happychriss/GoodWatch_espif_ESP-NN/src/my_RTC_DS3231.cpp

#include <my_RTClib.h>
#include "support.h"

#define DS3231_ADDRESS 0x68   ///< I2C address for DS3231
#define DS3231_TIME 0x00      ///< Time register
#define DS3231_ALARM1 0x07    ///< Alarm 1 register
#define DS3231_ALARM2 0x0B    ///< Alarm 2 register
#define DS3231_CONTROL 0x0E   ///< Control register
#define DS3231_STATUSREG 0x0F ///< Status register
#define DS3231_TEMPERATUREREG                                                  \
  0x11 ///< Temperature register (high byte - low byte is at 0x12), 10-bit
///< temperature value

/**************************************************************************/
/*!
    @brief  Start I2C for the DS3231 and test succesful connection
    @param  wireInstance pointer to the I2C bus
    @return True if Wire can find DS3231 or false otherwise.
*/
/**************************************************************************/
boolean RTC_DS3231::begin(TwoWire *wireInstance) {
    if (i2c_dev)
        delete i2c_dev;
    i2c_dev = new Adafruit_I2CDevice(DS3231_ADDRESS, wireInstance);
    if (!i2c_dev->begin())
        return false;
    return true;
}

/**************************************************************************/
/*!
    @brief  Check the status register Oscillator Stop Flag to see if the DS3231
   stopped due to power loss
    @return True if the bit is set (oscillator stopped) or false if it is
   running
*/
/**************************************************************************/
bool RTC_DS3231::lostPower(void) {
    return read_register(DS3231_STATUSREG) >> 7;
}

/**************************************************************************/
/*!
    @brief  Set the date and flip the Oscillator Stop Flag
    @param dt DateTime object containing the date/time to set
*/
/**************************************************************************/
void RTC_DS3231::adjust(const DateTime &dt) {
    uint8_t buffer[8] = {DS3231_TIME,
                         bin2bcd(dt.second()),
                         bin2bcd(dt.minute()),
                         bin2bcd(dt.hour()),
                         bin2bcd(dowToDS3231(dt.dayOfTheWeek())),
                         bin2bcd(dt.day()),
                         bin2bcd(dt.month()),
                         bin2bcd(dt.year() - 2000U)};
    i2c_dev->write(buffer, 8);

    uint8_t statreg = read_register(DS3231_STATUSREG);
    statreg &= ~0x80; // flip OSF bit
    write_register(DS3231_STATUSREG, statreg);
}

/**************************************************************************/
/*!
    @brief  Get the current date/time
    @return DateTime object with the current date/time
*/
/**************************************************************************/
DateTime RTC_DS3231::now() {
    uint8_t buffer[7];
    buffer[0] = 0;
    i2c_dev->write_then_read(buffer, 1, buffer, 7);

    return DateTime(bcd2bin(buffer[6]) + 2000U, bcd2bin(buffer[5] & 0x7F),
                    bcd2bin(buffer[4]), bcd2bin(buffer[2]), bcd2bin(buffer[1]),
                    bcd2bin(buffer[0] & 0x7F));
}

/**************************************************************************/
/*!
    @brief  Read the SQW pin mode
    @return Pin mode, see Ds3231SqwPinMode enum
*/
/**************************************************************************/
Ds3231SqwPinMode RTC_DS3231::readSqwPinMode() {
    int mode;
    mode = read_register(DS3231_CONTROL) & 0x1C;
    if (mode & 0x04)
        mode = DS3231_OFF;
    return static_cast<Ds3231SqwPinMode>(mode);
}

/**************************************************************************/
/*!
    @brief  Set the SQW pin mode
    @param mode Desired mode, see Ds3231SqwPinMode enum
*/
/**************************************************************************/
void RTC_DS3231::writeSqwPinMode(Ds3231SqwPinMode mode) {
    uint8_t ctrl = read_register(DS3231_CONTROL);

    ctrl &= ~0x04; // turn off INTCON
    ctrl &= ~0x18; // set freq bits to 0

    write_register(DS3231_CONTROL, ctrl | mode);
}

/**************************************************************************/
/*!
    @brief  Get the current temperature from the DS3231's temperature sensor
    @return Current temperature (float)
*/
/**************************************************************************/
float RTC_DS3231::getTemperature() {
    uint8_t buffer[2] = {DS3231_TEMPERATUREREG, 0};
    i2c_dev->write_then_read(buffer, 1, buffer, 2);
    return (float) buffer[0] + (buffer[1] >> 6) * 0.25f;
}

/**************************************************************************/
/*!
    @brief  Set alarm 1 for DS3231
        @param 	dt DateTime object
        @param 	alarm_mode Desired mode, see Ds3231Alarm1Mode enum
    @return False if control register is not set, otherwise true
*/
/**************************************************************************/
bool RTC_DS3231::setAlarm1(const DateTime &dt, Ds3231Alarm1Mode alarm_mode) {
    uint8_t ctrl = read_register(DS3231_CONTROL);
    if (!(ctrl & 0x04)) {
        return false;
    }

    uint8_t A1M1 = (alarm_mode & 0x01) << 7; // Seconds bit 7.
    uint8_t A1M2 = (alarm_mode & 0x02) << 6; // Minutes bit 7.
    uint8_t A1M3 = (alarm_mode & 0x04) << 5; // Hour bit 7.
    uint8_t A1M4 = (alarm_mode & 0x08) << 4; // Day/Date bit 7.
    uint8_t DY_DT = (alarm_mode & 0x10)
            << 2; // Day/Date bit 6. Date when 0, day of week when 1.
    uint8_t day = (DY_DT) ? dowToDS3231(dt.dayOfTheWeek()) : dt.day();

    uint8_t buffer[5] = {DS3231_ALARM1, uint8_t(bin2bcd(dt.second()) | A1M1),
                         uint8_t(bin2bcd(dt.minute()) | A1M2),
                         uint8_t(bin2bcd(dt.hour()) | A1M3),
                         uint8_t(bin2bcd(day) | A1M4 | DY_DT)};
    i2c_dev->write(buffer, 5);

    write_register(DS3231_CONTROL, ctrl | 0x01); // AI1E

    return true;
}

/**************************************************************************/
/*!
    @brief  Set alarm 2 for DS3231
        @param 	dt DateTime object
        @param 	alarm_mode Desired mode, see Ds3231Alarm2Mode enum
    @return False if control register is not set, otherwise true
*/
/**************************************************************************/
bool RTC_DS3231::setAlarm2(const DateTime &dt, Ds3231Alarm2Mode alarm_mode) {
    uint8_t ctrl = read_register(DS3231_CONTROL);
    if (!(ctrl & 0x04)) {
        DPL("ERROR: I2C Read Control Register");
        return false;
    }

    uint8_t A2M2 = (alarm_mode & 0x01) << 7; // Minutes bit 7.
    uint8_t A2M3 = (alarm_mode & 0x02) << 6; // Hour bit 7.
    uint8_t A2M4 = (alarm_mode & 0x04) << 5; // Day/Date bit 7.
    uint8_t DY_DT = (alarm_mode & 0x08)
            << 3; // Day/Date bit 6. Date when 0, day of week when 1.
    uint8_t day = (DY_DT) ? dowToDS3231(dt.dayOfTheWeek()) : dt.day();

    uint8_t buffer[4] = {DS3231_ALARM2, uint8_t(bin2bcd(dt.minute()) | A2M2),
                         uint8_t(bin2bcd(dt.hour()) | A2M3),
                         uint8_t(bin2bcd(day) | A2M4 | DY_DT)};

    if (!(i2c_dev->write(buffer, 4))) {
        DPL("ERROR: I2C Write Buffer");
        return false;
    };

    write_register(DS3231_CONTROL, ctrl | 0x02); // AI2E

    return true;
}

/**************************************************************************/
/*!
    @brief  Disable alarm
        @param 	alarm_num Alarm number to disable
*/
/**************************************************************************/
void RTC_DS3231::disableAlarm(uint8_t alarm_num) {
    uint8_t ctrl = read_register(DS3231_CONTROL);
    ctrl &= ~(1 << (alarm_num - 1));
    write_register(DS3231_CONTROL, ctrl);
}

/**************************************************************************/
/*!
    @brief  Clear status of alarm
        @param 	alarm_num Alarm number to clear
*/
/**************************************************************************/
void RTC_DS3231::clearAlarm(uint8_t alarm_num) {
    uint8_t status = read_register(DS3231_STATUSREG);
    status &= ~(0x1 << (alarm_num - 1));
    write_register(DS3231_STATUSREG, status);
}

/**************************************************************************/
/*!
    @brief  Get status of alarm
        @param 	alarm_num Alarm number to check status of
        @return True if alarm has been fired otherwise false
*/
/**************************************************************************/
bool RTC_DS3231::alarmFired(uint8_t alarm_num) {
    return (read_register(DS3231_STATUSREG) >> (alarm_num - 1)) & 0x1;
}

/**************************************************************************/
/*!
    @brief  Enable 32KHz Output
    @details The 32kHz output is enabled by default. It requires an external
    pull-up resistor to function correctly
*/
/**************************************************************************/
void RTC_DS3231::enable32K(void) {
    uint8_t status = read_register(DS3231_STATUSREG);
    status |= (0x1 << 0x03);
    write_register(DS3231_STATUSREG, status);
}

/**************************************************************************/
/*!
    @brief  Disable 32KHz Output
*/
/**************************************************************************/
void RTC_DS3231::disable32K(void) {
    uint8_t status = read_register(DS3231_STATUSREG);
    status &= ~(0x1 << 0x03);
    write_register(DS3231_STATUSREG, status);
}

/**************************************************************************/
/*!
    @brief  Get status of 32KHz Output
    @return True if enabled otherwise false
*/
/**************************************************************************/
bool RTC_DS3231::isEnabled32K(void) {
    return (read_register(DS3231_STATUSREG) >> 0x03) & 0x01;
}


bool RTC_DS3231::getAlarm2(DateTime *alarm, DateTime current_time) {

    DPL("Check Alarm2");
#define BM_ALARM_2_ENABLED  0b00000010
    uint8_t c = read_register(DS3231_CONTROL);
    boolean cc = (c & BM_ALARM_2_ENABLED) >> 1;

    if (cc) {
        DPL("Alarm2 is enabled!");
    } else {
        DPL("Alarm2 is disabled!");
    }

    uint8_t buffer[3] = {DS3231_ALARM2, 121, 122};
    if(!(i2c_dev->write_then_read(buffer, 1, buffer, 3,false))) {
        DPL("ERROR WRITE");
    }

    uint8_t m = buffer[0];
    uint8_t h = buffer[1];
    uint8_t d = buffer[2];

#define  BM_01_MIN 0b00001111
#define  BM_10_MIN 0b01110000
    uint8_t mm = (m & BM_01_MIN) + 10 * ((m & BM_10_MIN) >> 4);

#define BM_01_HH 0b00001111
#define BM_10_HH 0b00010000
#define BM_20_HH 0b00100000
    uint8_t hh = (h & BM_01_HH) + 10 * ((h & BM_10_HH) >> 4) + 20 * ((h & BM_20_HH) >> 5);

    // !!! Assuming date alarm is active
#define BM_01_DATE 0b00001111
#define BM_10_DATE 0b00110000
    uint8_t dd = (d & BM_01_DATE) + 10 * ((d & BM_10_DATE) >> 4);

    uint16_t yy = current_time.year();
    uint8_t mo = current_time.month();

    // Alarm clock does not know month, we can take current month/year - if alarm is on next month/month end, we need to jump to next month
    if (current_time.day() > dd) {
        mo++;
        if (mo > 12) {
            mo = 1;
            yy++;
        }
    }
    *alarm = DateTime(yy, mo, dd, hh, mm, 0);

    DPL("***********************");
    DPF("M:%i H:%i D:%i\n", m, h, d);
    DPF("%i:%i  - DD:%i MM:%i YY:%i \n", hh, mm, dd, mm, yy);
    DPL("***********************");

    return cc;

}


bool RTC_DS3231::getAlarm1(DateTime *alarm, DateTime current_time) {
    DPL("Check Alarm1");
#define BM_ALARM_2_ENABLED  0b00000010
#define BM_ALARM_1_ENABLED  0b00000001
    uint8_t c = read_register(DS3231_CONTROL);
    boolean cc = (c & BM_ALARM_1_ENABLED) ;

    if (cc) {
        DPL("Alarm1 is enabled!");
    } else {
        DPL("Alarm1 is disabled!");
    }


    uint8_t buffer[5] = {DS3231_ALARM1, 0, 0, 0,0};
    i2c_dev->write_then_read(buffer, 1, buffer, 3);

    uint8_t s = buffer[1];
    uint8_t m = buffer[2];
    uint8_t h = buffer[3];
    uint8_t d = buffer[4];

    DPF("Alarm1 s:%i,m:%i h:%i d:%i\n", s, m, h, d);

#define  BM_01_MIN 0b00001111
#define  BM_10_MIN 0b01110000
    uint8_t ss = (s & BM_01_MIN) + 10 * ((s & BM_10_MIN) >> 4);

#define  BM_01_MIN 0b00001111
#define  BM_10_MIN 0b01110000
    uint8_t mm = (m & BM_01_MIN) + 10 * ((m & BM_10_MIN) >> 4);

#define BM_01_HH 0b00001111
#define BM_10_HH 0b00010000
#define BM_20_HH 0b00100000
    uint8_t hh = (h & BM_01_HH) + 10 * ((h & BM_10_HH) >> 4) + 20 * ((h & BM_20_HH) >> 5);

    // !!! Assuming date alarm is active
#define BM_01_DATE 0b00001111
#define BM_10_DATE 0b00110000
    uint8_t dd = (d & BM_01_DATE) + 10 * ((d & BM_10_DATE) >> 4);

    uint16_t yy = current_time.year();
    uint8_t mo = current_time.month();

    // Alarm clock does not know month, we can take current month/year - if alarm is on next month/month end, we need to jump to next month
    if (current_time.day() > dd) {
        mo++;
        if (mo > 12) {
            mo = 1;
            yy++;
        }
    }
    *alarm = DateTime(yy, mo, dd, hh, mm, ss);

//        DPL("***********************");
    Serial.printf("S:%i M:%i H:%i D:%i\n", s,m, h, d);
    Serial.printf("%i:%i:%i  - DD:%i MO:%i YY:%i \n", hh, mm,ss, dd, mo, yy);
    DPL("***********************");

    return cc;

}
