happychriss/GoodWatch_espif_ESP-NN/include/GxEPD2_display_selection_new_style.h

// Display Library example for SPI e-paper panels from Dalian Good Display and boards from Waveshare.
// Requires HW SPI and Adafruit_GFX. Caution: the e-paper panels require 3.3V supply AND data lines!
//
// Display Library based on Demo Example from Good Display: http://www.e-paper-display.com/download_list/downloadcategoryid=34&isMode=false.html
//
// Author: Jean-Marc Zingg
//
// Version: see library.properties
//
// Library: https://github.com/ZinggJM/GxEPD2

// Supporting Arduino Forum Topics:
// Waveshare e-paper displays with SPI: http://forum.arduino.cc/index.php?topic=487007.0
// Good Display ePaper for Arduino: https://forum.arduino.cc/index.php?topic=436411.0

// select the display class (only one), matching the kind of display panel

//#undef DISABLE_DIAGNOSTIC_OUTPUT

#define GxEPD2_DISPLAY_CLASS GxEPD2_BW
//#define GxEPD2_DISPLAY_CLASS GxEPD2_3C
//#define GxEPD2_DISPLAY_CLASS GxEPD2_7C

// select the display driver class (only one) for your  panel
//#define GxEPD2_DRIVER_CLASS GxEPD2_154     // GDEP015OC1  200x200, no longer available
//#define GxEPD2_DRIVER_CLASS GxEPD2_154_D67 // GDEH0154D67 200x200
//#define GxEPD2_DRIVER_CLASS GxEPD2_154_T8  // GDEW0154T8  152x152
//#define GxEPD2_DRIVER_CLASS GxEPD2_154_M09 // GDEW0154M09 200x200
//#define GxEPD2_DRIVER_CLASS GxEPD2_154_M10 // GDEW0154M10 152x152
//#define GxEPD2_DRIVER_CLASS GxEPD2_213     // GDE0213B1   128x250, phased out
//#define GxEPD2_DRIVER_CLASS GxEPD2_213_B72 // GDEH0213B72 128x250
//#define GxEPD2_DRIVER_CLASS GxEPD2_213_B73 // GDEH0213B73 128x250
//#define GxEPD2_DRIVER_CLASS GxEPD2_213_flex // GDEW0213I5F 104x212
//#define GxEPD2_DRIVER_CLASS GxEPD2_213_M21 // GDEW0213M21 104x212
//#define GxEPD2_DRIVER_CLASS GxEPD2_213_T5D // GDEW0213T5D 104x212
//#define GxEPD2_DRIVER_CLASS GxEPD2_290     // GDEH029A1   128x296
//#define GxEPD2_DRIVER_CLASS GxEPD2_290_T5  // GDEW029T5   128x296
//#define GxEPD2_DRIVER_CLASS GxEPD2_290_T5D // GDEW029T5D  128x296
//#define GxEPD2_DRIVER_CLASS GxEPD2_290_T94 // GDEM029T94  128x296
//#define GxEPD2_DRIVER_CLASS GxEPD2_290_M06 // GDEW029M06  128x296
//#define GxEPD2_DRIVER_CLASS GxEPD2_260     // GDEW026T0   152x296
//#define GxEPD2_DRIVER_CLASS GxEPD2_260_M01 // GDEW026M01  152x296
//#define GxEPD2_DRIVER_CLASS GxEPD2_270     // GDEW027W3   176x264
//#define GxEPD2_DRIVER_CLASS GxEPD2_371     // GDEW0371W7  240x416
#define GxEPD2_DRIVER_CLASS GxEPD2_420     // GDEW042T2   400x300
//#define GxEPD2_DRIVER_CLASS GxEPD2_420_M01 // GDEW042M01  400x300
//#define GxEPD2_DRIVER_CLASS GxEPD2_583     // GDEW0583T7  600x448
//#define GxEPD2_DRIVER_CLASS GxEPD2_583_T8  // GDEW0583T8  648x480
//#define GxEPD2_DRIVER_CLASS GxEPD2_750     // GDEW075T8   640x384
//#define GxEPD2_DRIVER_CLASS GxEPD2_750_T7  // GDEW075T7   800x480
// 3-color e-papers
//#define GxEPD2_DRIVER_CLASS GxEPD2_154c     // GDEW0154Z04 200x200, no longer available
//#define GxEPD2_DRIVER_CLASS GxEPD2_154_Z90c // GDEH0154Z90 200x200
//#define GxEPD2_DRIVER_CLASS GxEPD2_213c     // GDEW0213Z16 104x212
//#define GxEPD2_DRIVER_CLASS GxEPD2_213_Z19c // GDEW0213Z19 104x212
//#define GxEPD2_DRIVER_CLASS GxEPD2_290c     // GDEW029Z10  128x296
//#define GxEPD2_DRIVER_CLASS GxEPD2_290_Z13c // GDEH029Z13  128x296
//#define GxEPD2_DRIVER_CLASS GxEPD2_290_C90c // GDEM029C90  128x296
//#define GxEPD2_DRIVER_CLASS GxEPD2_270c     // GDEW027C44  176x264
//#define GxEPD2_DRIVER_CLASS GxEPD2_420c     // GDEW042Z15  400x300
//#define GxEPD2_DRIVER_CLASS GxEPD2_583c     // GDEW0583Z21 600x448
//#define GxEPD2_DRIVER_CLASS GxEPD2_750c     // GDEW075Z09  640x384
//#define GxEPD2_DRIVER_CLASS GxEPD2_750c_Z08 // GDEW075Z08  800x480
//#define GxEPD2_DRIVER_CLASS GxEPD2_750c_Z90 // GDEH075Z90  880x528
//#define GxEPD2_DRIVER_CLASS GxEPD2_1248     // GDEW1248T3  1303x984
// 7-color e-paper
//#define GxEPD2_DRIVER_CLASS GxEPD2_565c // Waveshare 5.65" 7-color (3C graphics)
// grey levels parallel IF e-papers on Waveshare e-Paper IT8951 Driver HAT
//#define GxEPD2_DRIVER_CLASS GxEPD2_it60           // ED060SCT 800x600
//#define GxEPD2_DRIVER_CLASS GxEPD2_it60_1448x1072 // ED060KC1 1448x1072

// SS is usually used for CS. define here for easy change
#include <global_hardware.h>


#ifndef EPD_CS
#define EPD_CS SS
#endif

#if defined(GxEPD2_DISPLAY_CLASS) && defined(GxEPD2_DRIVER_CLASS)

// somehow there should be an easier way to do this
#define GxEPD2_BW_IS_GxEPD2_BW true
#define GxEPD2_3C_IS_GxEPD2_3C true
#define GxEPD2_7C_IS_GxEPD2_7C true
#define GxEPD2_1248_IS_GxEPD2_1248 true
#define IS_GxEPD(c, x) (c##x)
#define IS_GxEPD2_BW(x) IS_GxEPD(GxEPD2_BW_IS_, x)
#define IS_GxEPD2_3C(x) IS_GxEPD(GxEPD2_3C_IS_, x)
#define IS_GxEPD2_7C(x) IS_GxEPD(GxEPD2_7C_IS_, x)
#define IS_GxEPD2_1248(x) IS_GxEPD(GxEPD2_1248_IS_, x)

#include "GxEPD2_selection_check.h"

#if defined (ESP8266)
#define MAX_DISPLAY_BUFFER_SIZE (81920ul-34000ul-5000ul) // ~34000 base use, change 5000 to your application use
#if IS_GxEPD2_BW(GxEPD2_DISPLAY_CLASS)
#define MAX_HEIGHT(EPD) (EPD::HEIGHT <= MAX_DISPLAY_BUFFER_SIZE / (EPD::WIDTH / 8) ? EPD::HEIGHT : MAX_DISPLAY_BUFFER_SIZE / (EPD::WIDTH / 8))
#elif IS_GxEPD2_3C(GxEPD2_DISPLAY_CLASS)
#define MAX_HEIGHT(EPD) (EPD::HEIGHT <= (MAX_DISPLAY_BUFFER_SIZE / 2) / (EPD::WIDTH / 8) ? EPD::HEIGHT : (MAX_DISPLAY_BUFFER_SIZE / 2) / (EPD::WIDTH / 8))
#elif IS_GxEPD2_7C(GxEPD2_DISPLAY_CLASS)
#define MAX_HEIGHT(EPD) (EPD::HEIGHT <= (MAX_DISPLAY_BUFFER_SIZE) / (EPD::WIDTH / 2) ? EPD::HEIGHT : (MAX_DISPLAY_BUFFER_SIZE) / (EPD::WIDTH / 2))
#endif
// adapt the constructor parameters to your wiring
GxEPD2_DISPLAY_CLASS<GxEPD2_DRIVER_CLASS, MAX_HEIGHT(GxEPD2_DRIVER_CLASS)> display(GxEPD2_DRIVER_CLASS(/*CS=D8*/ EPD_CS, /*DC=D3*/ 0, /*RST=D4*/ 2, /*BUSY=D2*/ 4));
// mapping of Waveshare e-Paper ESP8266 Driver Board, new version
//GxEPD2_DISPLAY_CLASS<GxEPD2_DRIVER_CLASS, MAX_HEIGHT(GxEPD2_DRIVER_CLASS)> display(GxEPD2_DRIVER_CLASS(/*CS=15*/ EPD_CS, /*DC=4*/ 4, /*RST=2*/ 2, /*BUSY=5*/ 5));
// mapping of Waveshare e-Paper ESP8266 Driver Board, old version
//GxEPD2_DISPLAY_CLASS<GxEPD2_DRIVER_CLASS, MAX_HEIGHT(GxEPD2_DRIVER_CLASS)> display(GxEPD2_DRIVER_CLASS(/*CS=15*/ EPD_CS, /*DC=4*/ 4, /*RST=5*/ 5, /*BUSY=16*/ 16));
#endif

#if defined(ESP32)
#define MAX_DISPLAY_BUFFER_SIZE 65536ul // e.g.
#if IS_GxEPD2_BW(GxEPD2_DISPLAY_CLASS)
#define MAX_HEIGHT(EPD) (EPD::HEIGHT <= MAX_DISPLAY_BUFFER_SIZE / (EPD::WIDTH / 8) ? EPD::HEIGHT : MAX_DISPLAY_BUFFER_SIZE / (EPD::WIDTH / 8))
#elif IS_GxEPD2_3C(GxEPD2_DISPLAY_CLASS)
#define MAX_HEIGHT(EPD) (EPD::HEIGHT <= (MAX_DISPLAY_BUFFER_SIZE / 2) / (EPD::WIDTH / 8) ? EPD::HEIGHT : (MAX_DISPLAY_BUFFER_SIZE / 2) / (EPD::WIDTH / 8))
#elif IS_GxEPD2_7C(GxEPD2_DISPLAY_CLASS)
#define MAX_HEIGHT(EPD) (EPD::HEIGHT <= (MAX_DISPLAY_BUFFER_SIZE) / (EPD::WIDTH / 2) ? EPD::HEIGHT : (MAX_DISPLAY_BUFFER_SIZE) / (EPD::WIDTH / 2))
#endif
// adapt the constructor parameters to your wiring
#if !IS_GxEPD2_1248(GxEPD2_DRIVER_CLASS)
#if defined(ARDUINO_LOLIN_D32_PRO)
GxEPD2_DISPLAY_CLASS<GxEPD2_DRIVER_CLASS, MAX_HEIGHT(GxEPD2_DRIVER_CLASS)> display(GxEPD2_DRIVER_CLASS(/*CS=5*/ EPD_CS, /*DC=*/ EPD_DC, /*RST=*/ EPD_RST, /*BUSY=*/ EPD_BUSY));
#elif defined(ARDUINO_ESP32_DEV) // e.g. TTGO T8 ESP32-WROVER
GxEPD2_DISPLAY_CLASS<GxEPD2_DRIVER_CLASS, MAX_HEIGHT(GxEPD2_DRIVER_CLASS)> display(GxEPD2_DRIVER_CLASS(/*CS=5*/ EPD_CS, /*DC=*/ 2, /*RST=*/ 0, /*BUSY=*/ 4));
#else
GxEPD2_DISPLAY_CLASS<GxEPD2_DRIVER_CLASS, MAX_HEIGHT(GxEPD2_DRIVER_CLASS)> display(GxEPD2_DRIVER_CLASS(/*CS=5*/ EPD_CS, /*DC=*/ 17, /*RST=*/ 16, /*BUSY=*/ 4));
#endif
#else // GxEPD2_1248
// Waveshare 12.48 b/w SPI display board and frame or Good Display 12.48 b/w panel GDEW1248T3
// general constructor for use with all parameters, e.g. for Waveshare ESP32 driver board mounted on connection board
GxEPD2_BW < GxEPD2_1248, GxEPD2_1248::HEIGHT / 4 > display(GxEPD2_1248(/*sck=*/ 13, /*miso=*/ 12, /*mosi=*/ 14,
    /*cs_m1=*/ 23, /*cs_s1=*/ 22, /*cs_m2=*/ 16, /*cs_s2=*/ 19,
    /*dc1=*/ 25, /*dc2=*/ 17, /*rst1=*/ 33, /*rst2=*/ 5,
    /*busy_m1=*/ 32, /*busy_s1=*/ 26, /*busy_m2=*/ 18, /*busy_s2=*/ 4));
#endif
#endif

// can't use package "STMF1 Boards (STM32Duino.com)" (Roger Clark) anymore with Adafruit_GFX, use "STM32 Boards (selected from submenu)" (STMicroelectronics)
#if defined(ARDUINO_ARCH_STM32)
#define MAX_DISPLAY_BUFFER_SIZE 15000ul // ~15k is a good compromise
#if IS_GxEPD2_BW(GxEPD2_DISPLAY_CLASS)
#define MAX_HEIGHT(EPD) (EPD::HEIGHT <= MAX_DISPLAY_BUFFER_SIZE / (EPD::WIDTH / 8) ? EPD::HEIGHT : MAX_DISPLAY_BUFFER_SIZE / (EPD::WIDTH / 8))
#elif IS_GxEPD2_3C(GxEPD2_DISPLAY_CLASS)
#define MAX_HEIGHT(EPD) (EPD::HEIGHT <= (MAX_DISPLAY_BUFFER_SIZE / 2) / (EPD::WIDTH / 8) ? EPD::HEIGHT : (MAX_DISPLAY_BUFFER_SIZE / 2) / (EPD::WIDTH / 8))
#elif IS_GxEPD2_7C(GxEPD2_DISPLAY_CLASS)
#define MAX_HEIGHT(EPD) (EPD::HEIGHT <= (MAX_DISPLAY_BUFFER_SIZE) / (EPD::WIDTH / 2) ? EPD::HEIGHT : (MAX_DISPLAY_BUFFER_SIZE) / (EPD::WIDTH / 2))
#endif
// adapt the constructor parameters to your wiring
GxEPD2_DISPLAY_CLASS<GxEPD2_DRIVER_CLASS, MAX_HEIGHT(GxEPD2_DRIVER_CLASS)> display(GxEPD2_DRIVER_CLASS(/*CS=4*/ EPD_CS, /*DC=*/ 3, /*RST=*/ 2, /*BUSY=*/ 1));
#endif

#if defined(__AVR)
#if defined (ARDUINO_AVR_MEGA2560) // Note: SS is on 53 on MEGA
#define MAX_DISPLAY_BUFFER_SIZE 5000 // e.g. full height for 200x200
#else // Note: SS is on 10 on UNO, NANO
#define MAX_DISPLAY_BUFFER_SIZE 800 // 
#endif
#if IS_GxEPD2_BW(GxEPD2_DISPLAY_CLASS)
#define MAX_HEIGHT(EPD) (EPD::HEIGHT <= MAX_DISPLAY_BUFFER_SIZE / (EPD::WIDTH / 8) ? EPD::HEIGHT : MAX_DISPLAY_BUFFER_SIZE / (EPD::WIDTH / 8))
#elif IS_GxEPD2_3C(GxEPD2_DISPLAY_CLASS)
#define MAX_HEIGHT(EPD) (EPD::HEIGHT <= (MAX_DISPLAY_BUFFER_SIZE / 2) / (EPD::WIDTH / 8) ? EPD::HEIGHT : (MAX_DISPLAY_BUFFER_SIZE / 2) / (EPD::WIDTH / 8))
#elif IS_GxEPD2_7C(GxEPD2_DISPLAY_CLASS)
#define MAX_HEIGHT(EPD) (EPD::HEIGHT <= (MAX_DISPLAY_BUFFER_SIZE) / (EPD::WIDTH / 2) ? EPD::HEIGHT : (MAX_DISPLAY_BUFFER_SIZE) / (EPD::WIDTH / 2))
#endif
// adapt the constructor parameters to your wiring
GxEPD2_DISPLAY_CLASS<GxEPD2_DRIVER_CLASS, MAX_HEIGHT(GxEPD2_DRIVER_CLASS)> display(GxEPD2_DRIVER_CLASS(/*CS=*/ EPD_CS, /*DC=*/ 8, /*RST=*/ 9, /*BUSY=*/ 7));
#endif

#if defined(ARDUINO_ARCH_SAM)
#define MAX_DISPLAY_BUFFER_SIZE 32768ul // e.g., up to 96k
#if IS_GxEPD2_BW(GxEPD2_DISPLAY_CLASS)
#define MAX_HEIGHT(EPD) (EPD::HEIGHT <= MAX_DISPLAY_BUFFER_SIZE / (EPD::WIDTH / 8) ? EPD::HEIGHT : MAX_DISPLAY_BUFFER_SIZE / (EPD::WIDTH / 8))
#elif IS_GxEPD2_3C(GxEPD2_DISPLAY_CLASS)
#define MAX_HEIGHT(EPD) (EPD::HEIGHT <= (MAX_DISPLAY_BUFFER_SIZE / 2) / (EPD::WIDTH / 8) ? EPD::HEIGHT : (MAX_DISPLAY_BUFFER_SIZE / 2) / (EPD::WIDTH / 8))
#elif IS_GxEPD2_7C(GxEPD2_DISPLAY_CLASS)
#define MAX_HEIGHT(EPD) (EPD::HEIGHT <= (MAX_DISPLAY_BUFFER_SIZE) / (EPD::WIDTH / 2) ? EPD::HEIGHT : (MAX_DISPLAY_BUFFER_SIZE) / (EPD::WIDTH / 2))
#endif
// adapt the constructor parameters to your wiring
GxEPD2_DISPLAY_CLASS<GxEPD2_DRIVER_CLASS, MAX_HEIGHT(GxEPD2_DRIVER_CLASS)> display(GxEPD2_DRIVER_CLASS(/*CS=77*/ EPD_CS, /*DC=*/ 8, /*RST=*/ 9, /*BUSY=*/ 7));
#endif

#if defined(ARDUINO_ARCH_SAMD)
#define MAX_DISPLAY_BUFFER_SIZE 15000ul // ~15k is a good compromise
#if IS_GxEPD2_BW(GxEPD2_DISPLAY_CLASS)
#define MAX_HEIGHT(EPD) (EPD::HEIGHT <= MAX_DISPLAY_BUFFER_SIZE / (EPD::WIDTH / 8) ? EPD::HEIGHT : MAX_DISPLAY_BUFFER_SIZE / (EPD::WIDTH / 8))
#elif IS_GxEPD2_3C(GxEPD2_DISPLAY_CLASS)
#define MAX_HEIGHT(EPD) (EPD::HEIGHT <= (MAX_DISPLAY_BUFFER_SIZE / 2) / (EPD::WIDTH / 8) ? EPD::HEIGHT : (MAX_DISPLAY_BUFFER_SIZE / 2) / (EPD::WIDTH / 8))
#elif IS_GxEPD2_7C(GxEPD2_DISPLAY_CLASS)
#define MAX_HEIGHT(EPD) (EPD::HEIGHT <= (MAX_DISPLAY_BUFFER_SIZE) / (EPD::WIDTH / 2) ? EPD::HEIGHT : (MAX_DISPLAY_BUFFER_SIZE) / (EPD::WIDTH / 2))
#endif
// adapt the constructor parameters to your wiring
GxEPD2_DISPLAY_CLASS<GxEPD2_DRIVER_CLASS, MAX_HEIGHT(GxEPD2_DRIVER_CLASS)> display(GxEPD2_DRIVER_CLASS(/*CS=4*/ 4, /*DC=*/ 7, /*RST=*/ 6, /*BUSY=*/ 5));
#endif

#endif
