happychriss/GoodWatch_espif_ESP-NN/src/audio_support.h

//
// Created by development on 13.11.21.
//

#ifndef GOODWATCH_AUDIO_SUPPORT_H
#define GOODWATCH_AUDIO_SUPPORT_H

extern bool b_audio_end_of_mp3;
extern bool b_pir_wave;
extern bool b_audio_finished;
extern Audio audio;

void PlayWakeupSong();
#endif //GOODWATCH_AUDIO_SUPPORT_H
