happychriss/GoodWatch_espif_ESP-NN/src/wifi_support.h

//
// Created by development on 05.11.21.
//

#ifndef GOODWATCH_WIFI_SUPPORT_H
#define GOODWATCH_WIFI_SUPPORT_H
#include <WiFi.h>
#include "WiFiCredentials.h"
#include "WiFiClient.h"
#include <HTTPClient.h>
#include <lwip/apps/sntp.h>
#include "support.h"
void SetupWifi_SNTP() ;
void sendData(uint8_t *bytes, size_t count);
#endif //GOODWATCH_WIFI_SUPPORT_H
